Narain-Vazquez/AeroGuard-Project/Software/Code source/Frontend code/bg.png

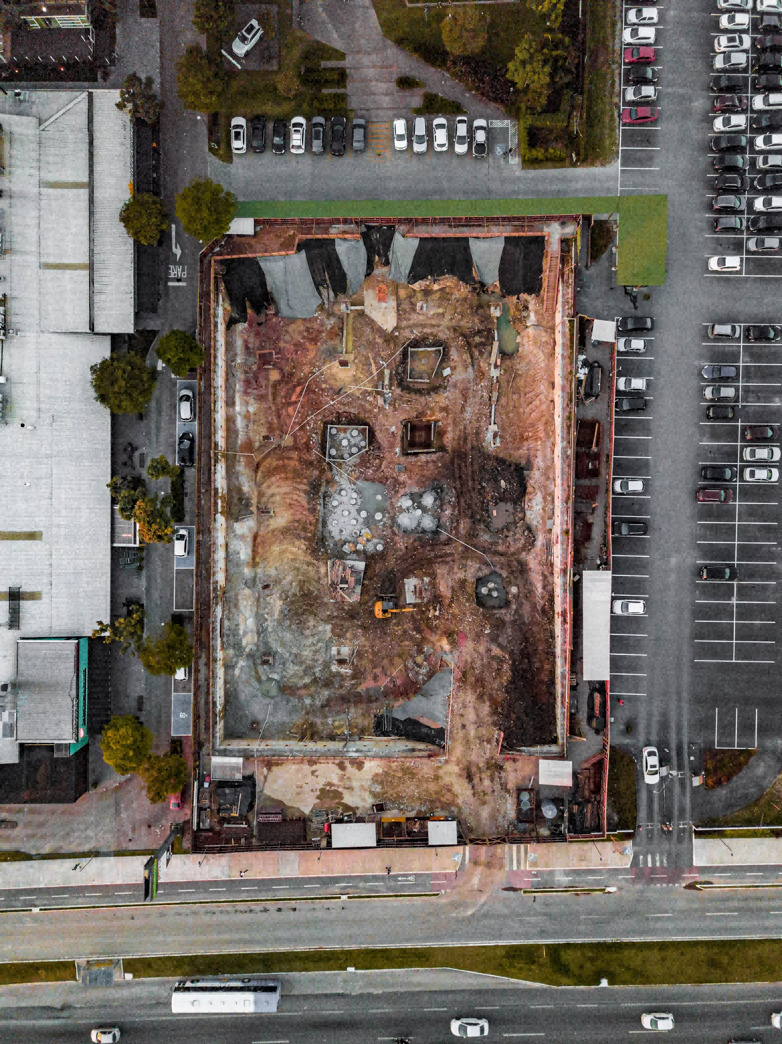
Software/Code source/Frontend code/bg.png
