Narain-Vazquez/AeroGuard-Project/Software/Software files/Flowcharts/Alarm Handler flowchar.png

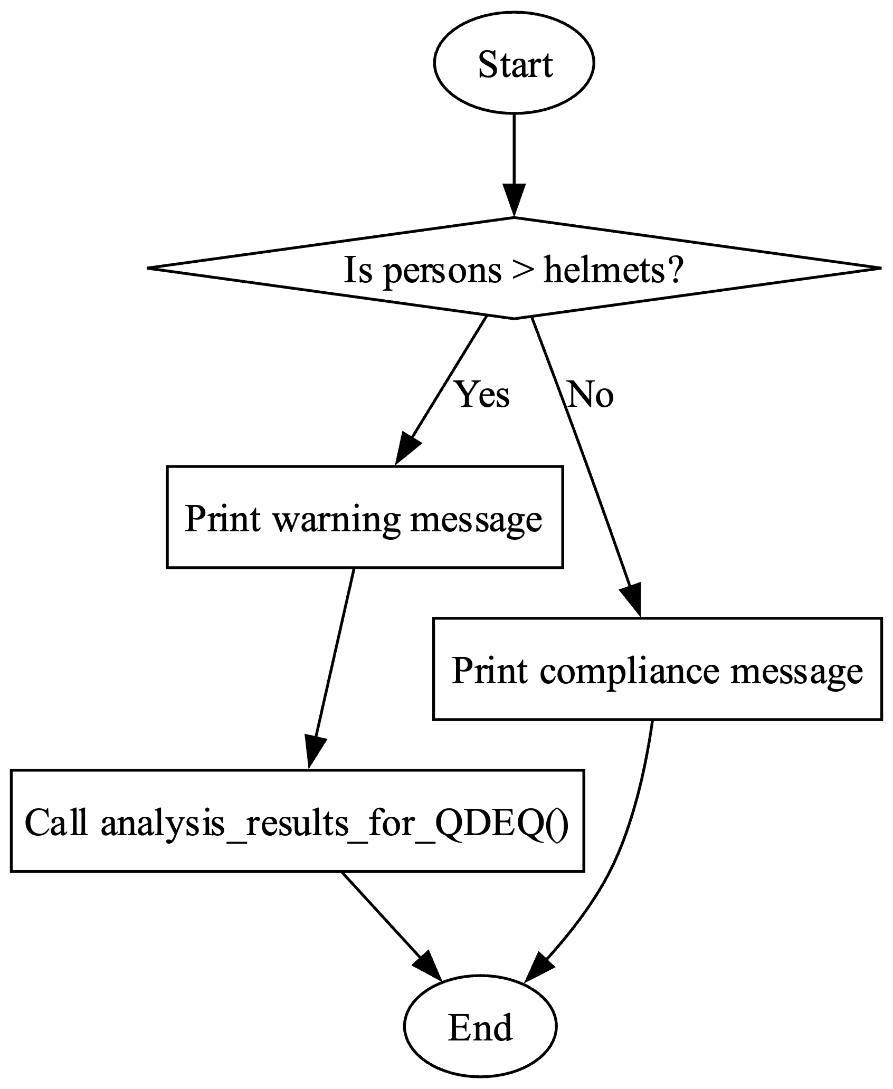
Software/Software files/Flowcharts/Alarm Handler flowchar.png
