Narain-Vazquez/AeroGuard-Project/Software/Software files/Flowcharts/Alarm State Transition Diagram.png

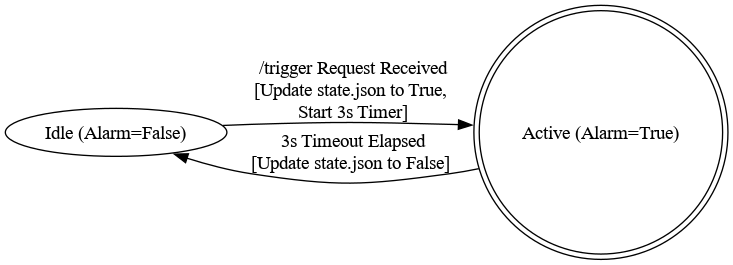
Software/Software files/Flowcharts/Alarm State Transition Diagram.png
