Narain-Vazquez/AeroGuard-Project/Software/Software files/Flowcharts/Data Uploader flowchart.png

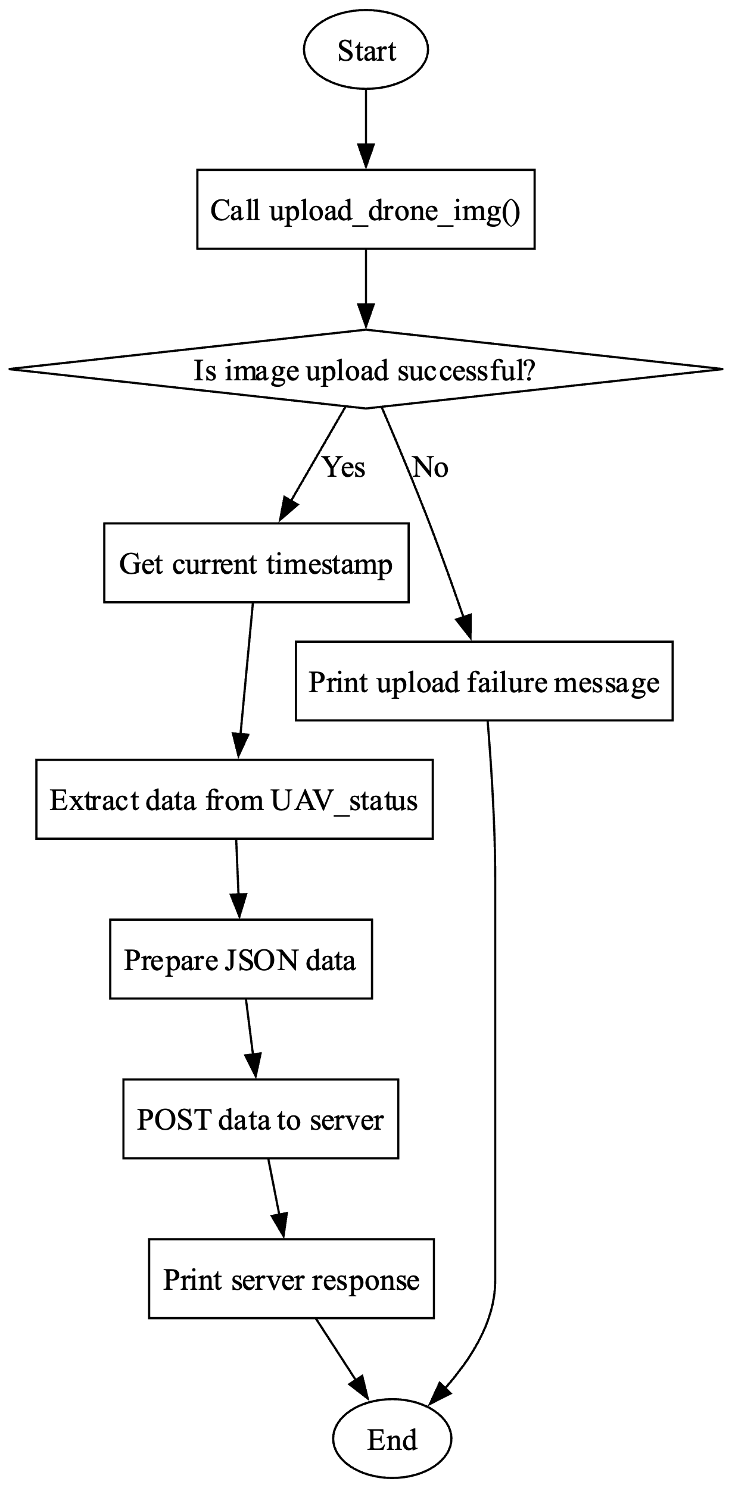
Software/Software files/Flowcharts/Data Uploader flowchart.png
