Narain-Vazquez/AeroGuard-Project/Software/Software files/Flowcharts/Detection Handler flowchart.png

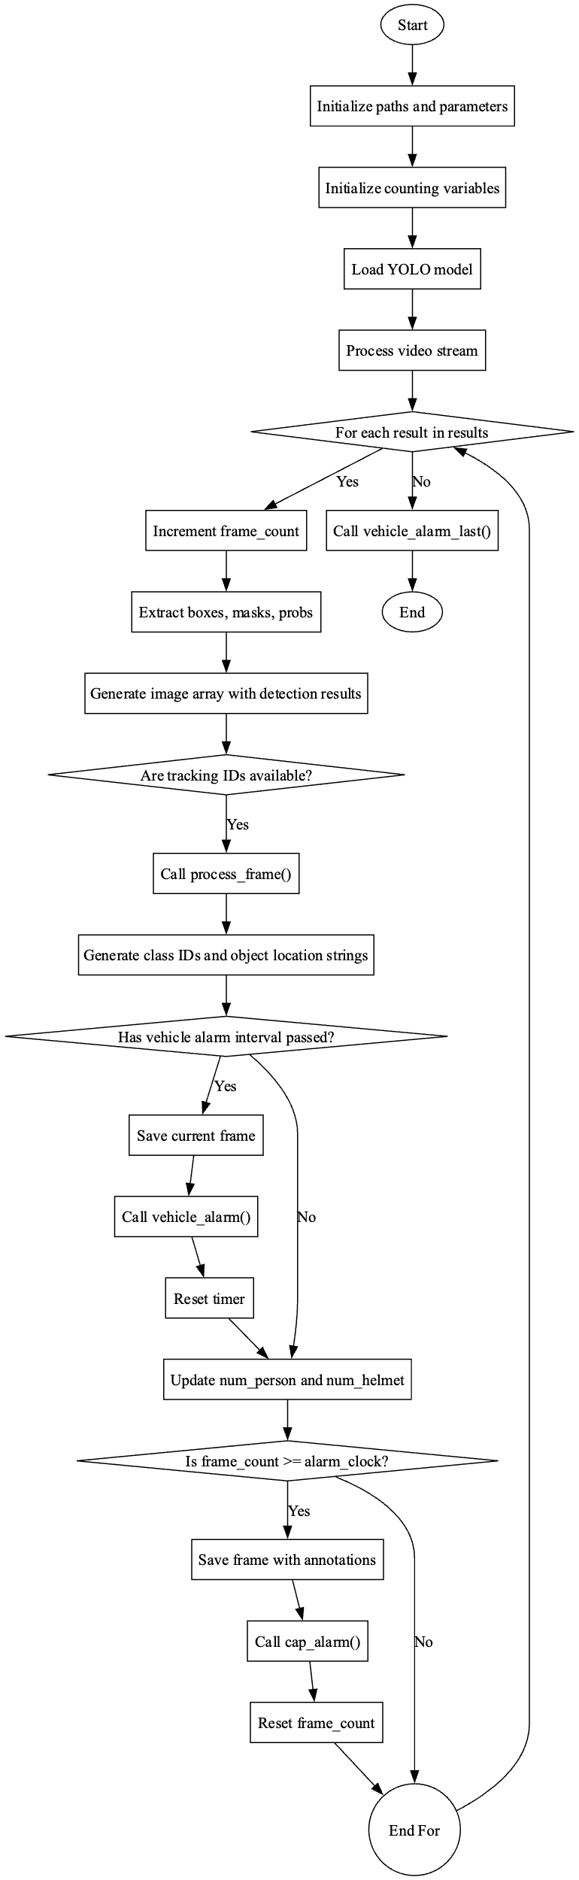
Software/Software files/Flowcharts/Detection Handler flowchart.png
