Narain-Vazquez/AeroGuard-Project/Software/Software files/Flowcharts/Drawing Utility flowchart.png

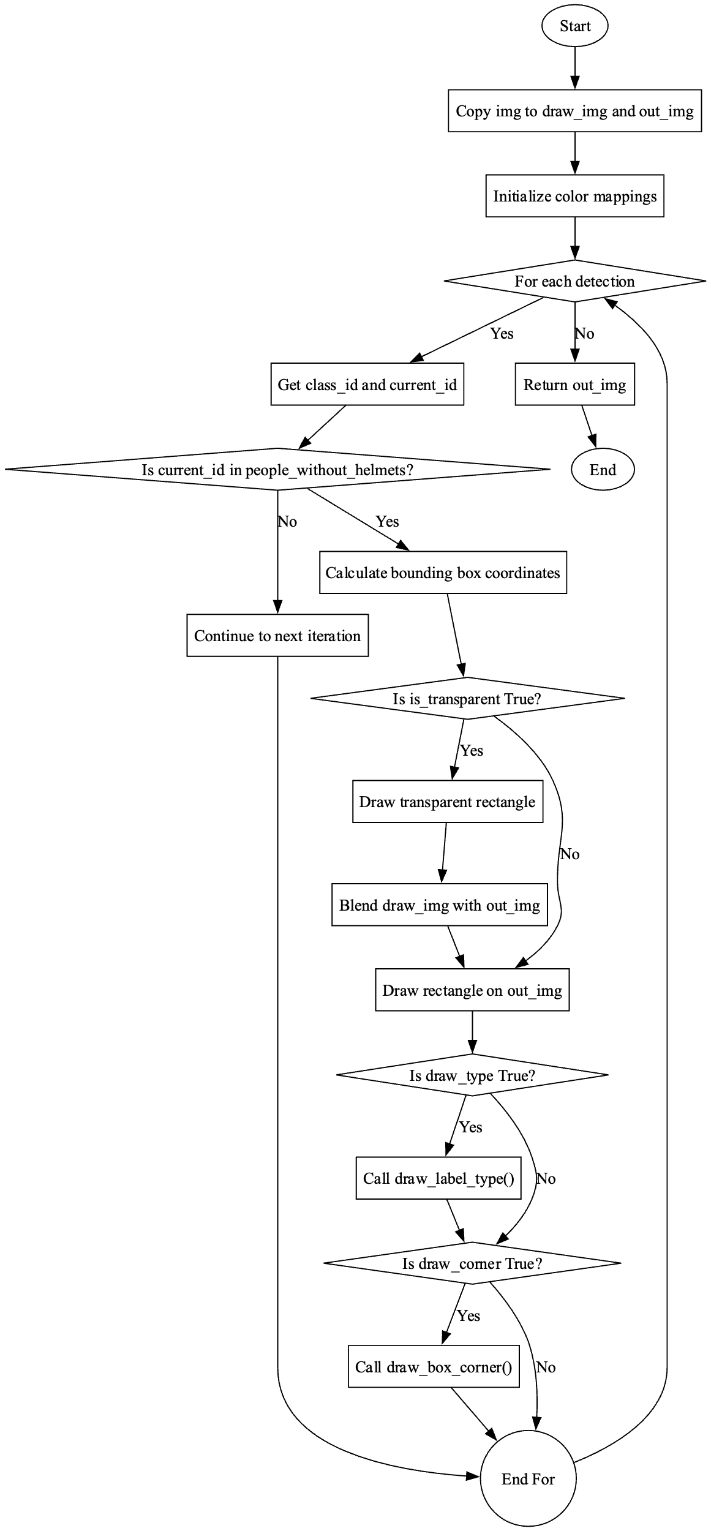
Software/Software files/Flowcharts/Drawing Utility flowchart.png
