Narain-Vazquez/AeroGuard-Project/Software/Software files/Flowcharts/Frame Processor flowchart.png

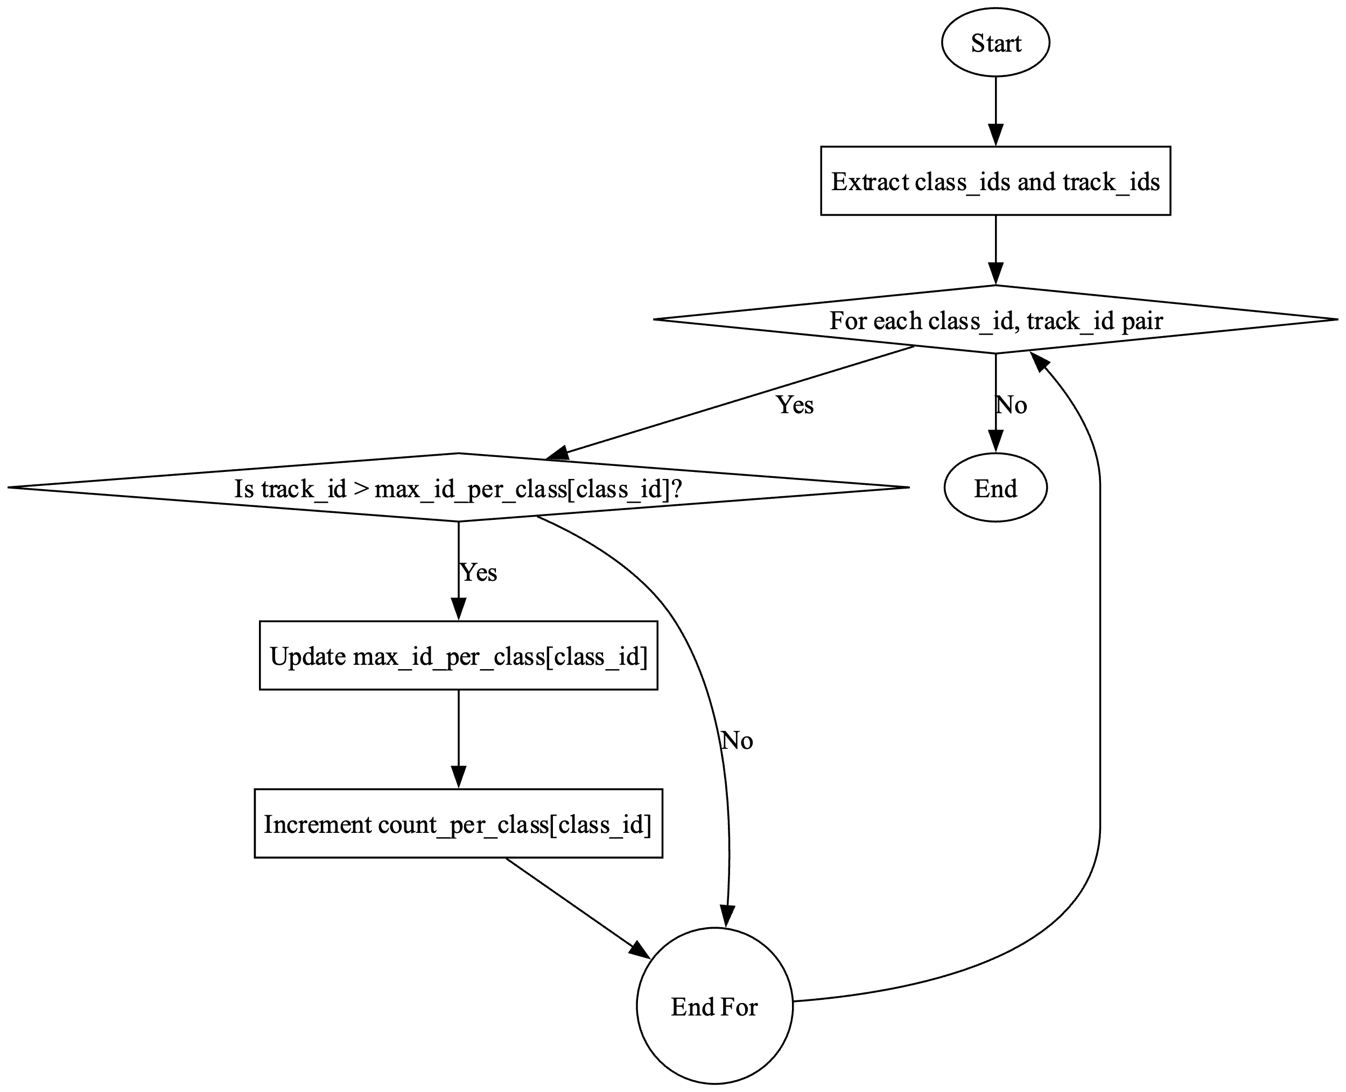
Software/Software files/Flowcharts/Frame Processor flowchart.png
