Narain-Vazquez/AeroGuard-Project/Software/Software files/Flowcharts/helper_utilities_flowchart.png

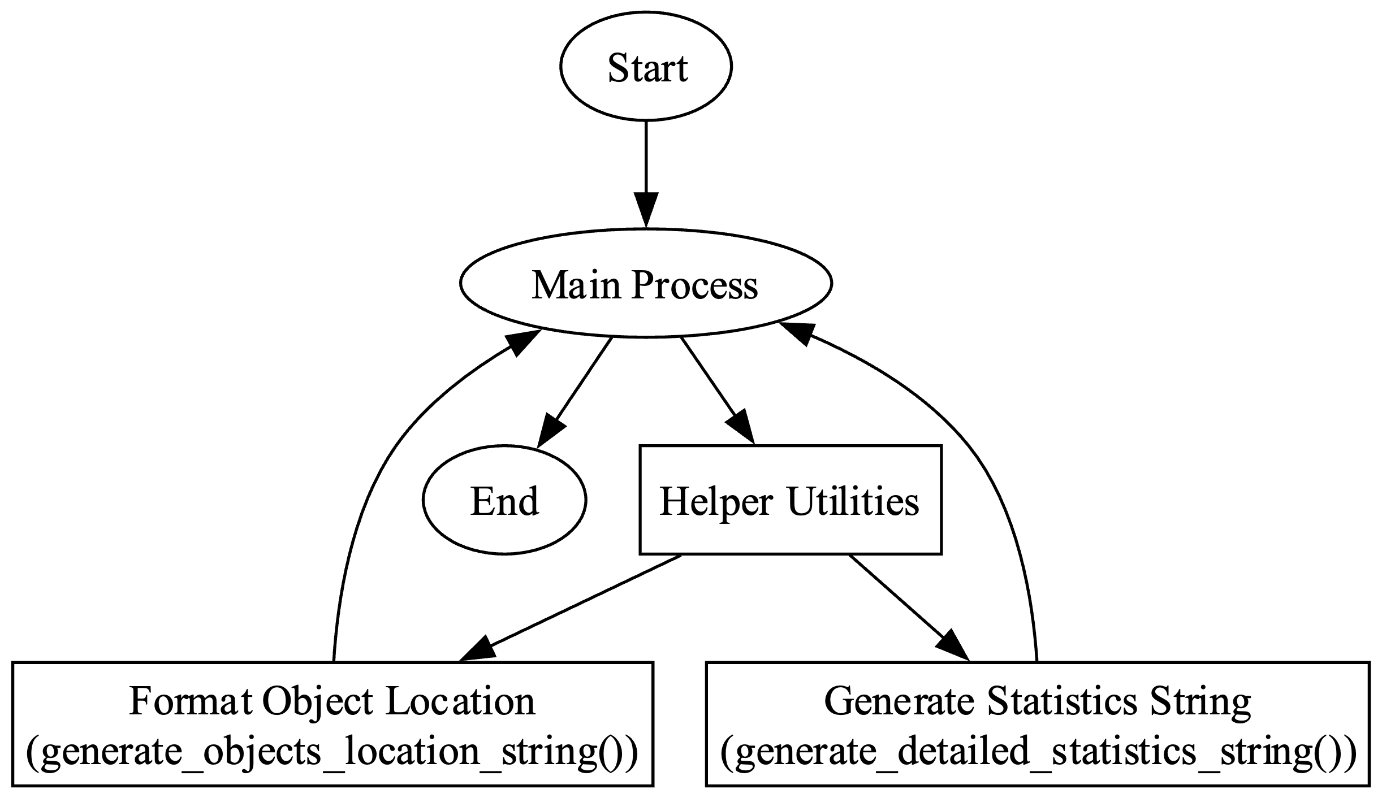
Software/Software files/Flowcharts/helper_utilities_flowchart.png
