Narain-Vazquez/AeroGuard-Project/Software/Software files/Flowcharts/Image Uploader flowchart.png

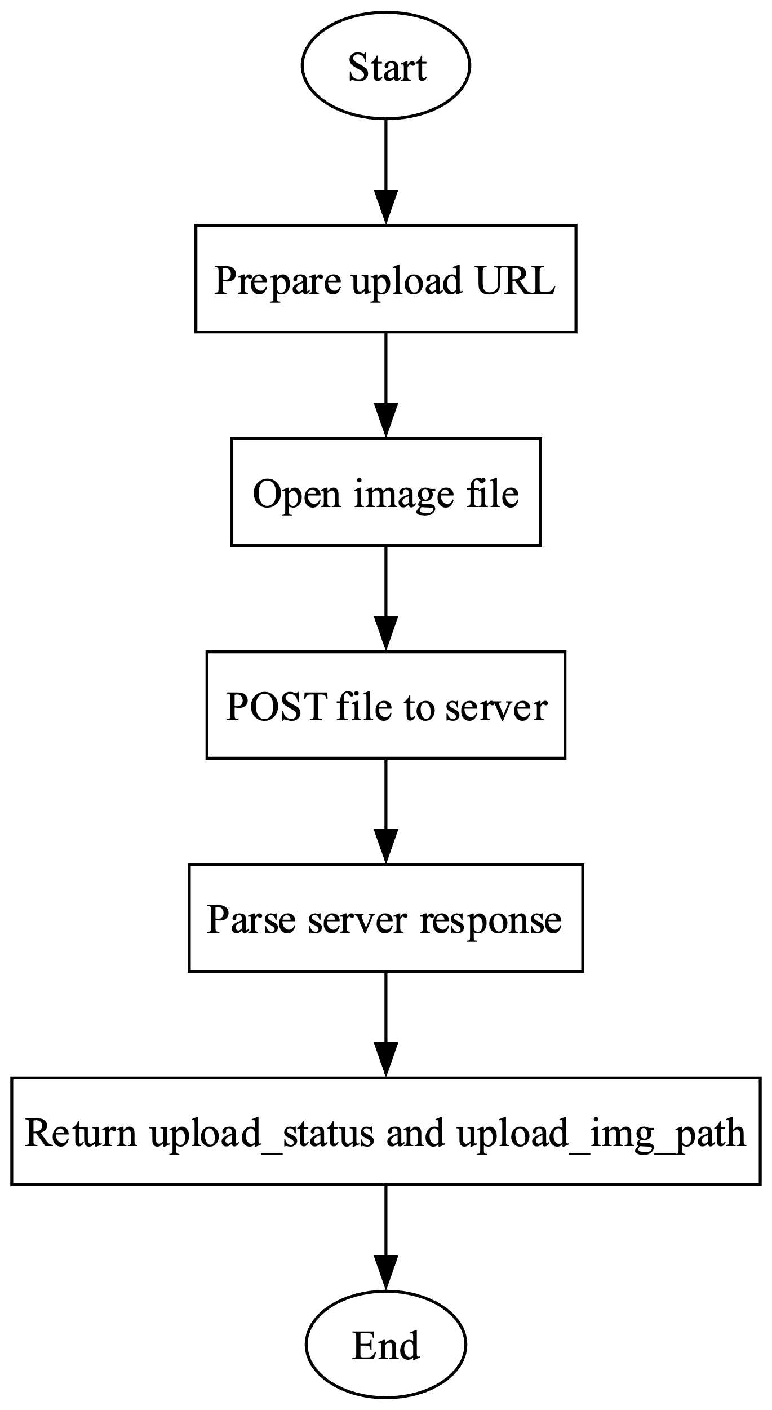
Software/Software files/Flowcharts/Image Uploader flowchart.png
