Narain-Vazquez/AeroGuard-Project/Software/Software files/Flowcharts/Stream Handler flowchart.png

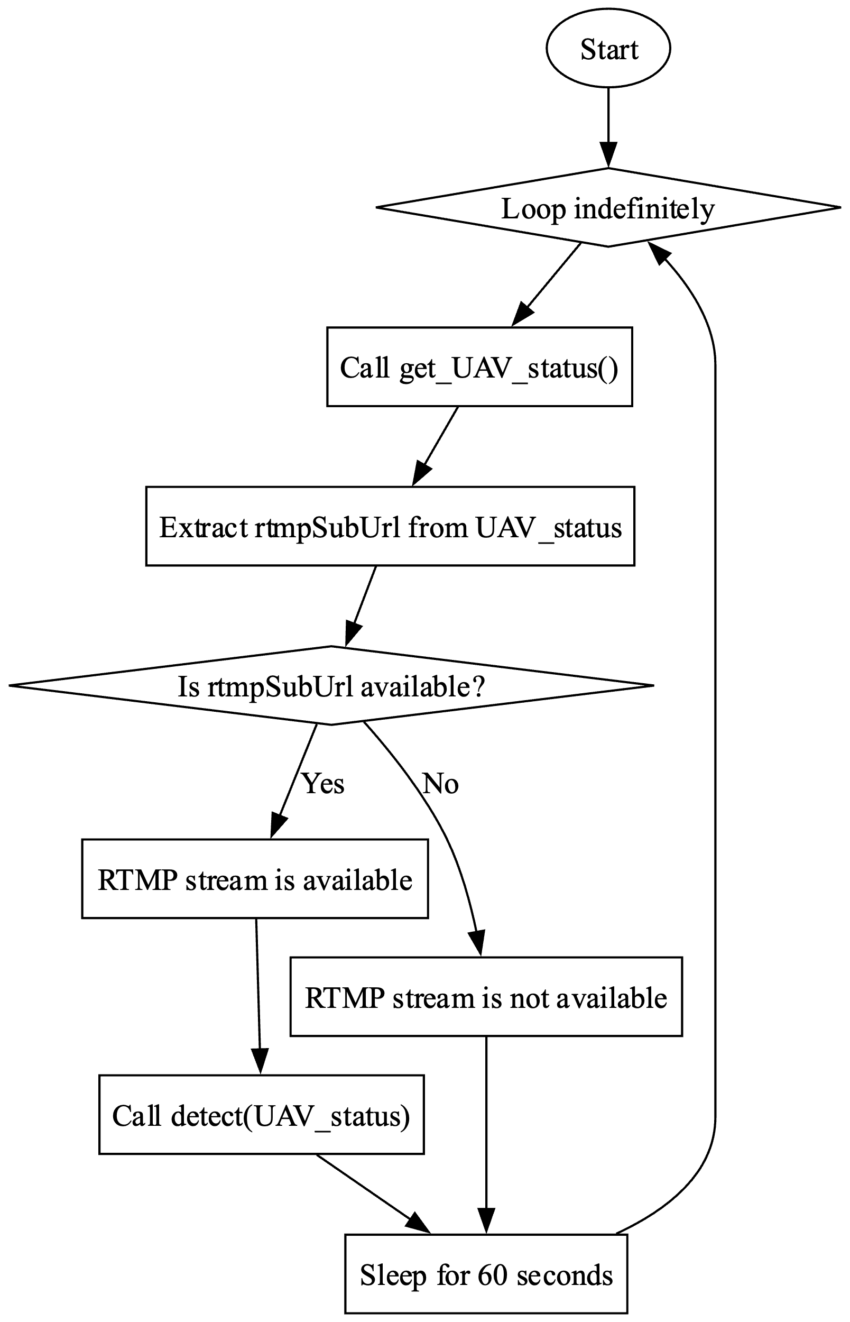
Software/Software files/Flowcharts/Stream Handler flowchart.png
