Narain-Vazquez/AeroGuard-Project/Software/Software files/Flowcharts/System Interface.jpg

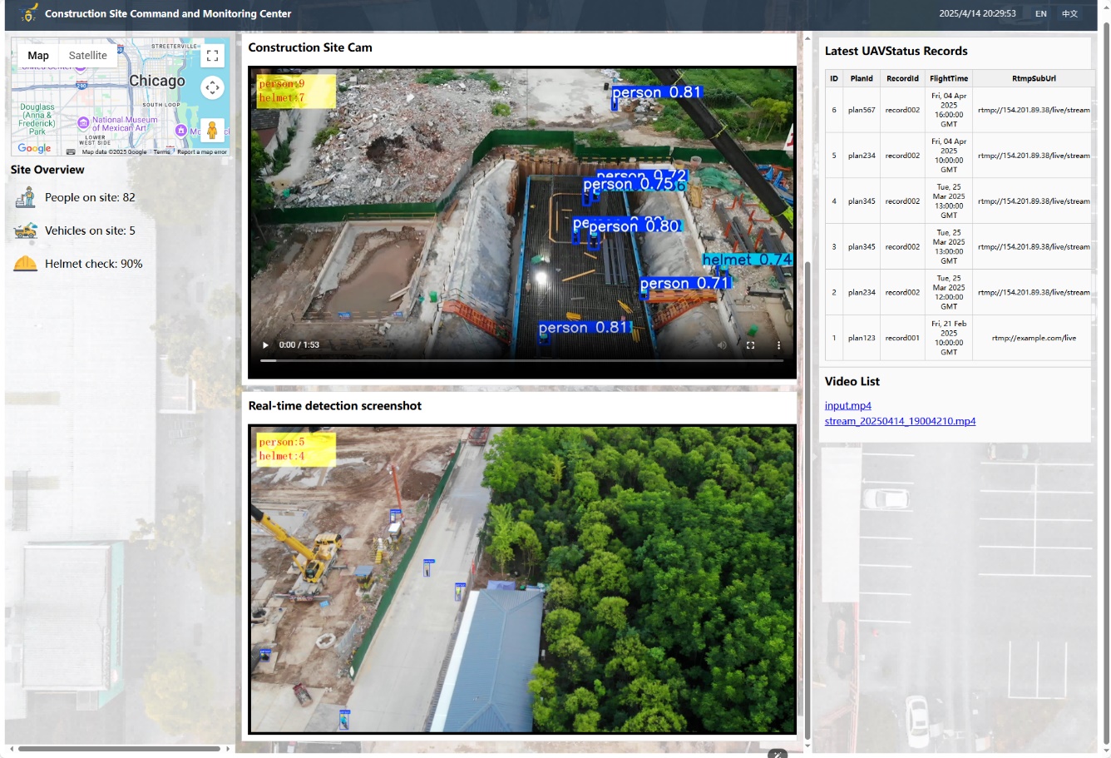
Software/Software files/Flowcharts/System Interface.jpg
