Narain-Vazquez/AeroGuard-Project/Software/Software files/Flowcharts/Validation Utility flowchart.png

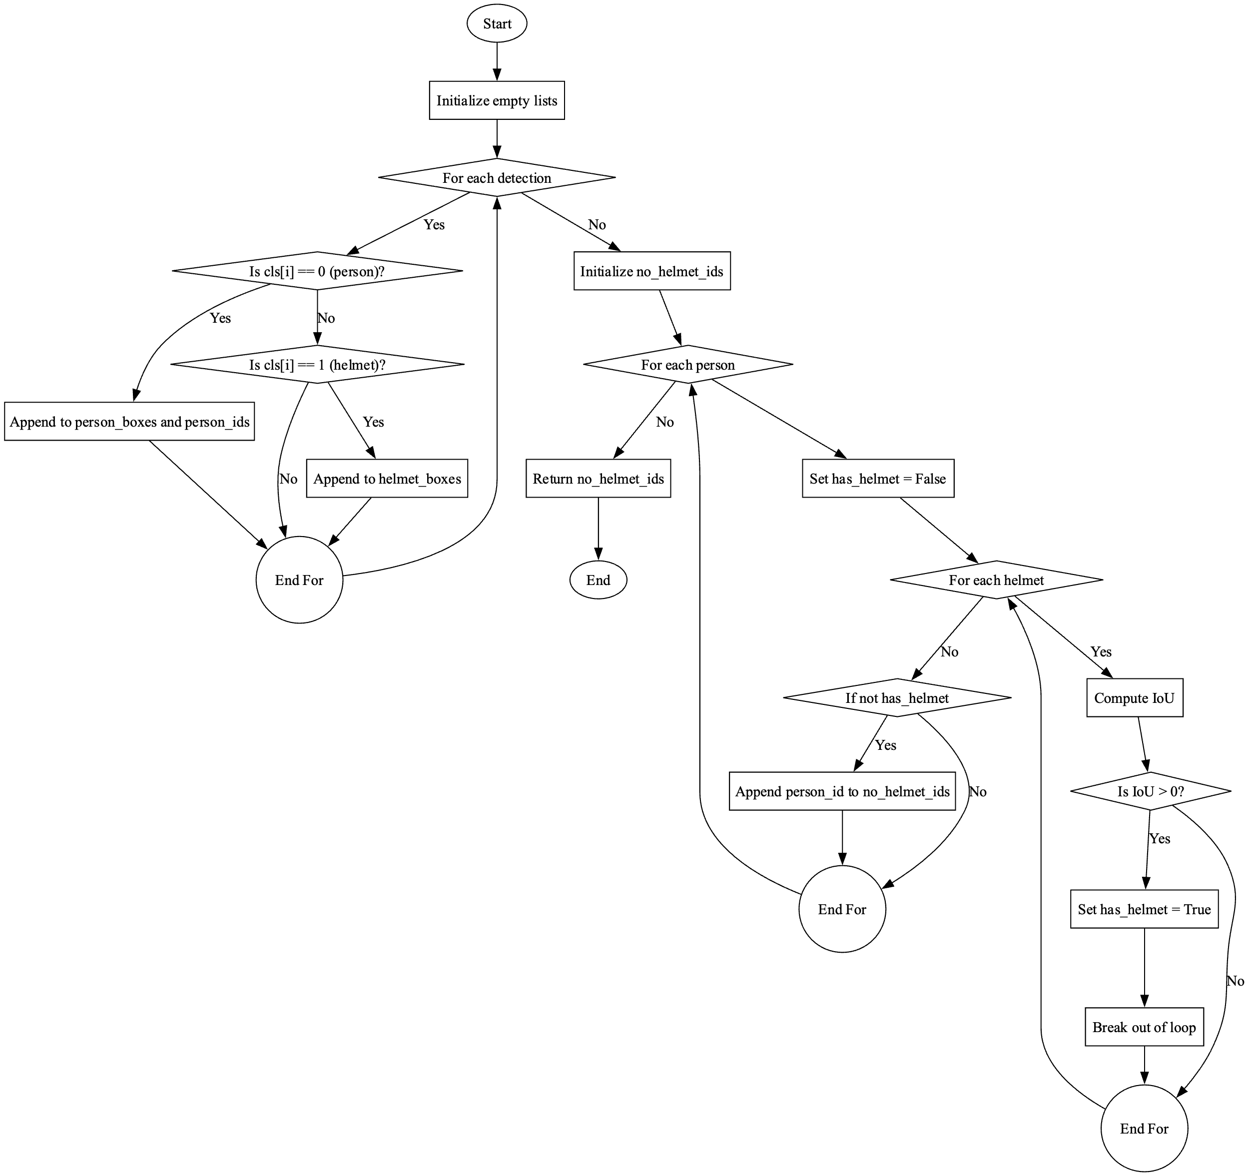
Software/Software files/Flowcharts/Validation Utility flowchart.png
