Narain-Vazquez/AeroGuard-Project/Software/Software files/Test data/Test images/helmet.png

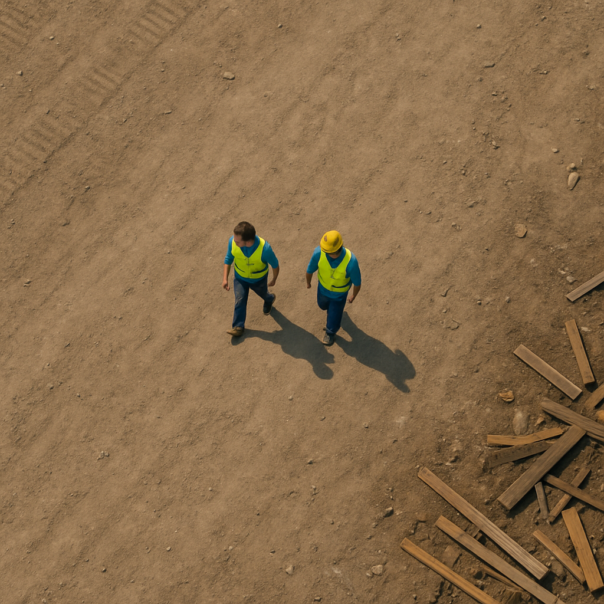
Software/Software files/Test data/Test images/helmet.png
