Narain-Vazquez/AeroGuard-Project/Software/Software files/Test data/Test images/test_helmet-flame.png

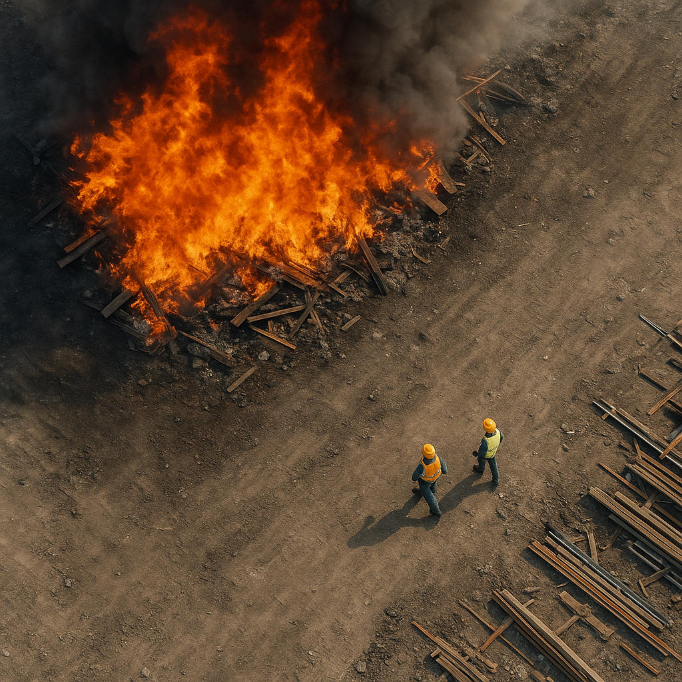
Software/Software files/Test data/Test images/test_helmet-flame.png
